mn89h/PiezoTestplatform/Presentation/Präsentation.pdf

Elektro- und Informationstechnik | Integrierte Elektronische Systeme | Malte Nilges

# DESIGN AND DEVELOPMENT OF A CUSTOM ASIC TEST PCB FOR ULTRASONIC COMMUNICATION

# Project seminar by

# Malte Nilges

12.08.2023 | 1

# OVERVIEW

# - Piezoelectric transducers for sensor communication and energy harvesting

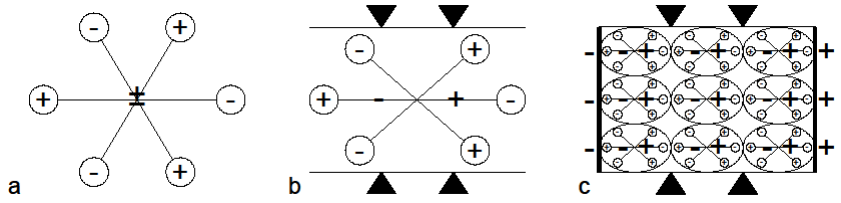
[picture p25: figure]

# - Aim of this work:

# - Piezo driver platform for data transmission and reception → hardware platform (PCB) → software platform (FPGA logic)

12.08.2023

C U S T O M A S I C T E S T P C B F O R U L T R A S O N I C C O M M U N I C A T I O N / M A L T E N I L G E S

# PCB DESIGN

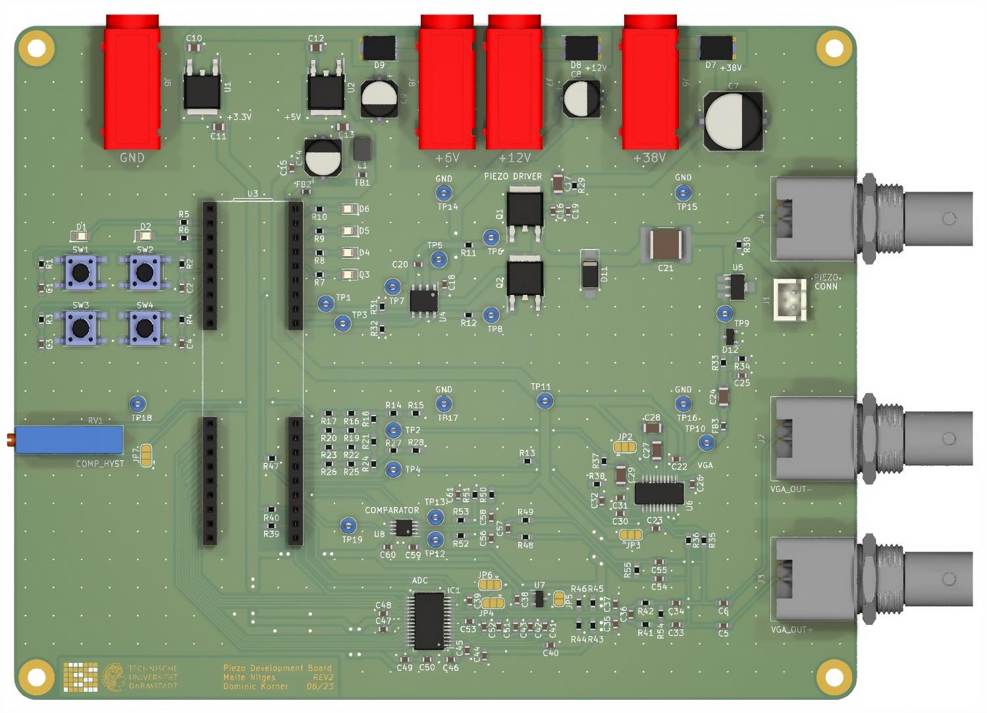
[picture p26: figure]

# PCB DESIGN

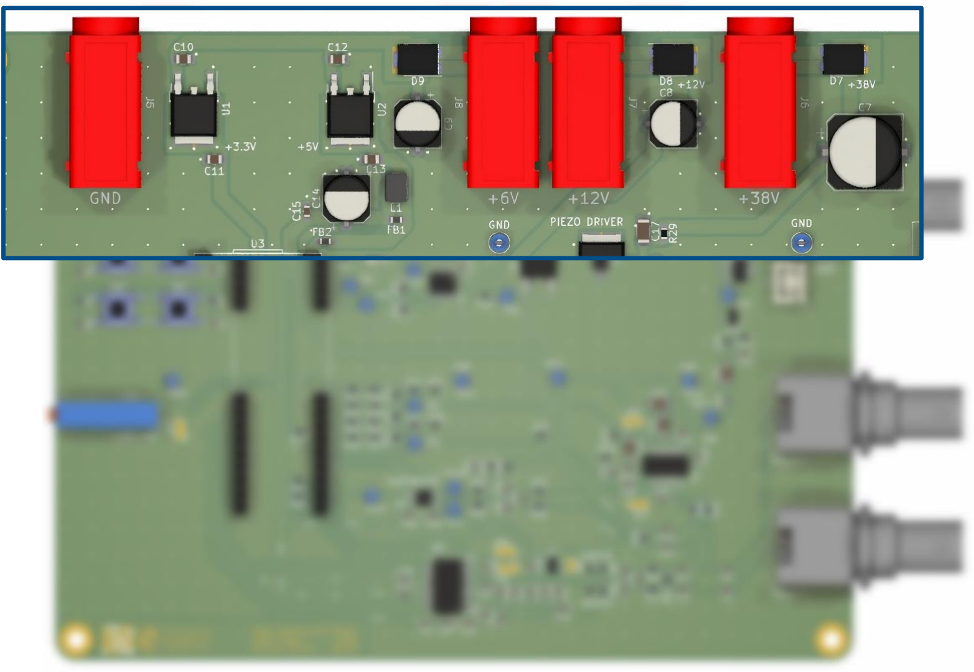
[picture p27: figure]

# Power stage:

# - Rails: 3.3V, 5VA, 5VD, 12V, 38V

# - NCP1117 3.3V & 5V LDO

# - 3 connectors

# - Reverse polarity protection diodes

# PCB DESIGN

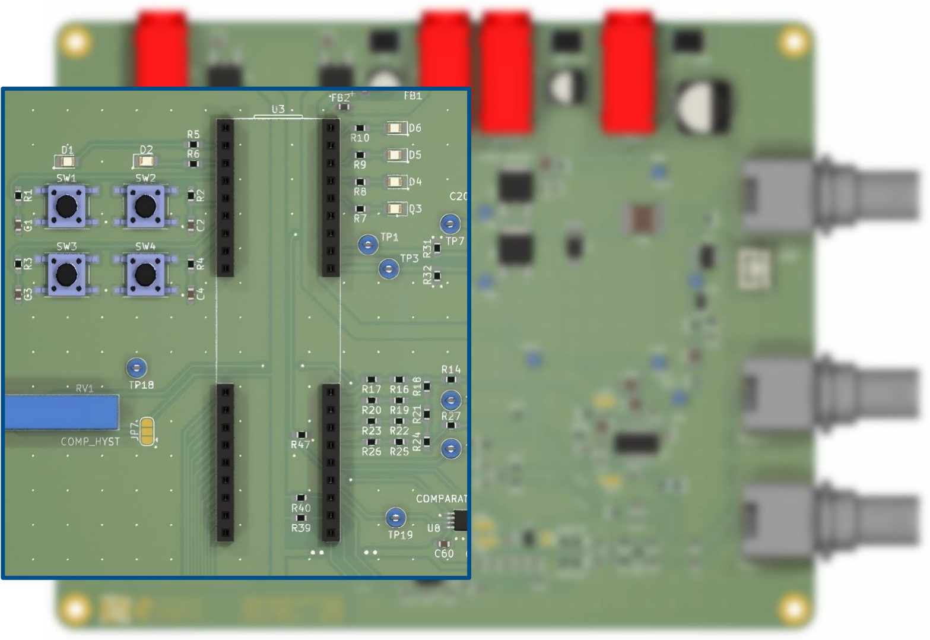
[picture p28: figure]

# FPGA & I/O:

# - CMOD S7 (Spartan XC7S25)

# - Push Buttons

# - LEDs

# - DAC

# PCB DESIGN

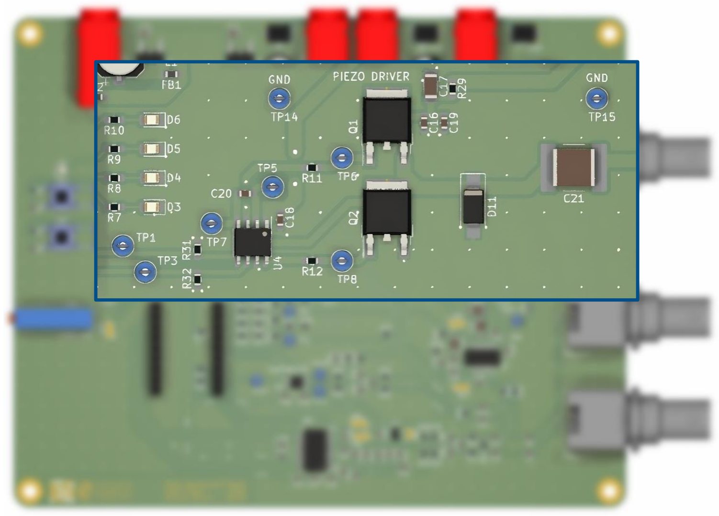
[picture p29: figure]

# Piezo driver stage:

# - MIC4604 half-bridge gate driver

# - 2x FDD1600N10ALZ NMOS

# - TVS diode

# - AC-coupled output

# PCB DESIGN

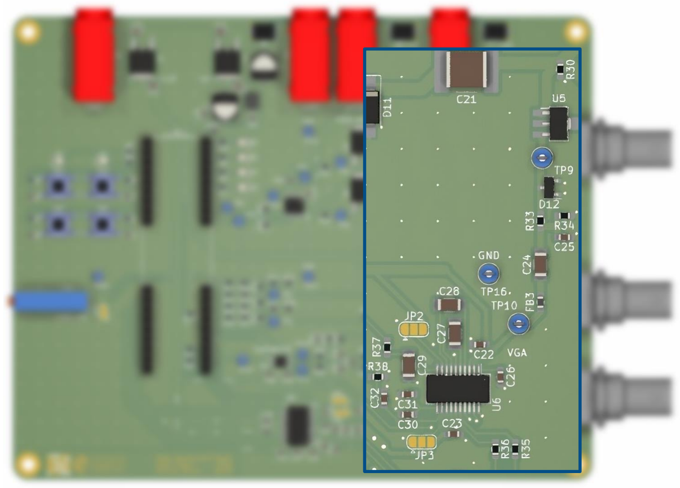
[picture p30: figure]

# Piezo input & amplifier stage:

# - MD0100 T/R switch

# - BAV99 protection diodes

# - Filtering network

# - AD8331 Low-Noise Amplifier with Variable Gain Amplifier

# PCB DESIGN

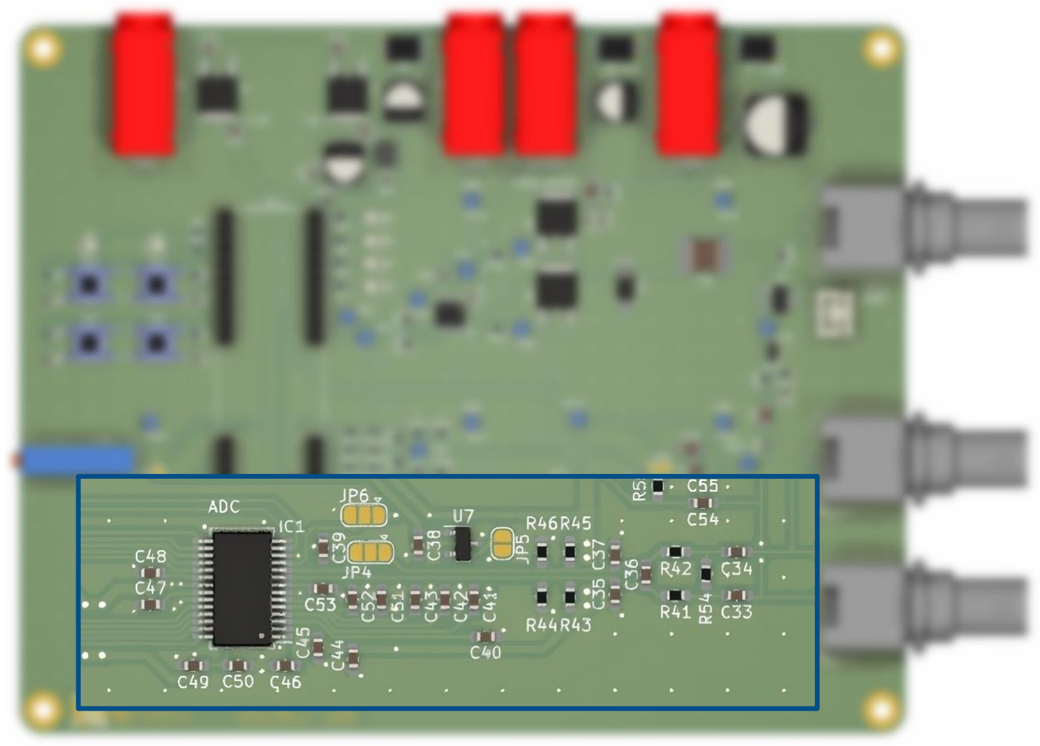
[picture p31: figure]

# ADC stage:

# - AC-coupled

# - Low-pass filter network

# - MAX1426 10bit 10MHz ADC

# - Internal biasing; Vpp,diff = 4V

# PCB DESIGN

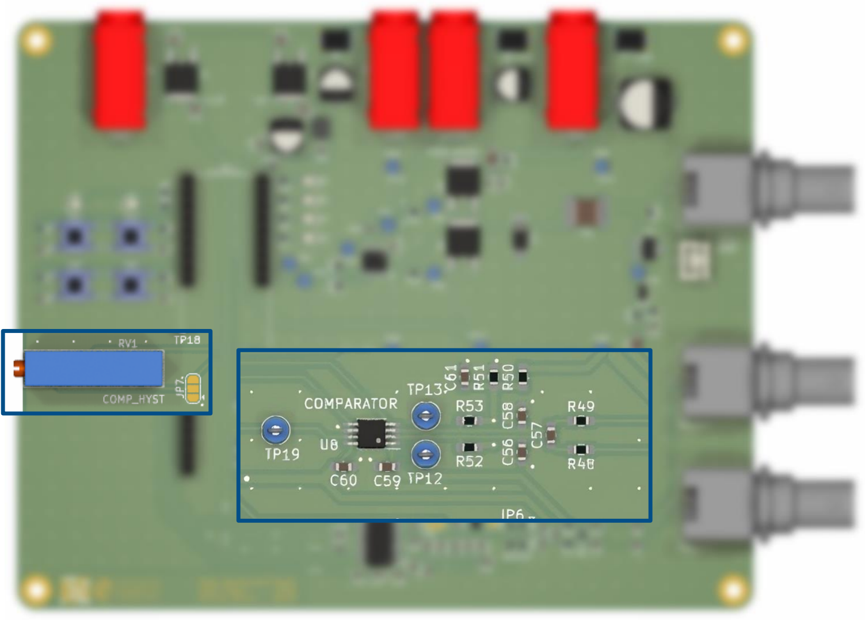
[picture p32: figure]

# Comparator stage:

# - AC-coupled

# - Band-pass filter network

# - LTC6752 280MHz comparator

# - External biasing

# - Adjustable hysteresis

# FPGA MODULES

# Main modules:

# - comm_protocol

# - vga_driver

# - comp_driver

# - adc_driver

Helper modules: | Imported modules:

# FPGA MODULES

# Helper modules:

# - piezo_driver

# - delay

# - fifo_aggregate

# - fifo_x2byte

# - pulse_stretcher

# - serial_tx_handler

# - serial_rx_handler

# - buttons_handler

# Main modules:

# - comm_protocol

# - vga_driver

# - comp_driver

# - adc_driver

# Imported modules:

# FPGA MODULES

# Helper modules:

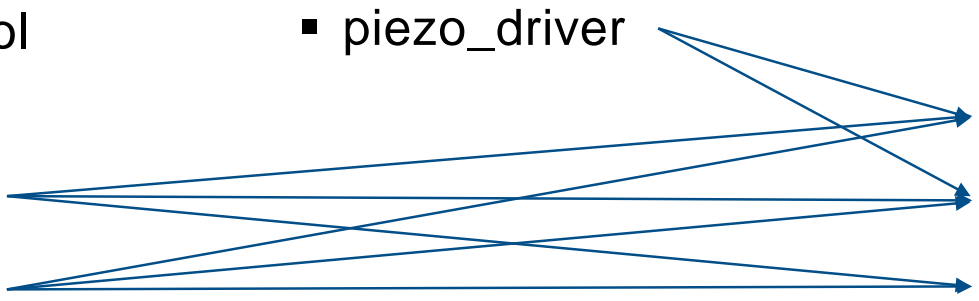
[picture p33: figure]
▪ piezo_driver

# - serial_tx_handler

# - serial_rx_handler

# Main modules:

# - comm_protocol

# - vga_driver

# - comp_driver

# - adc_driver

# Imported modules:

# - mmcme2_*

# - xpm_cdc_*

# - xpm_fifo_async

# - uart_tx

# - uart_rx

# RESULTS – TRANSMISSION

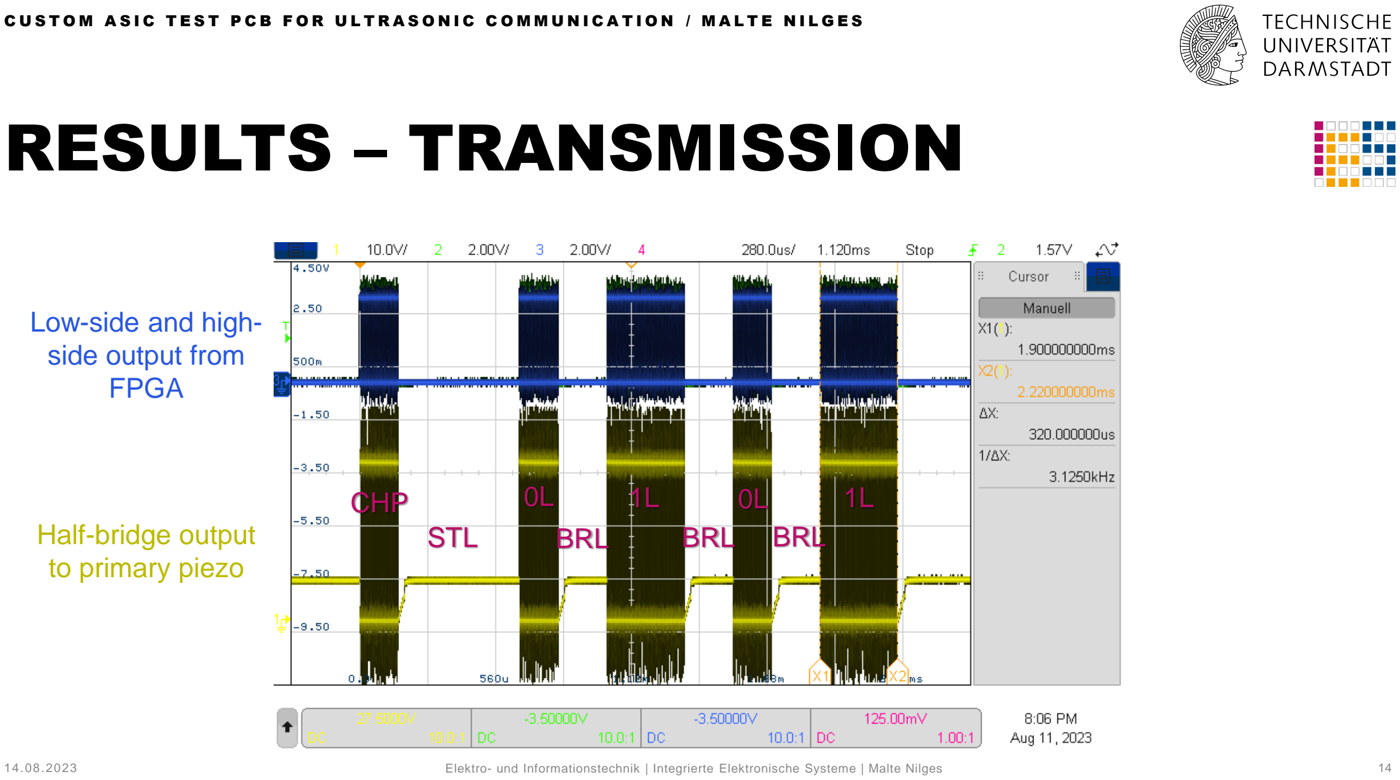
[picture p34: page 13]

# CHP STL

0L | 0L
BRL | BRL
1L | 1L
Half-bridge output | BRL

# to primary piezo

# Low-side and high-side output from FPGA

# RESULTS – TRANSMISSION

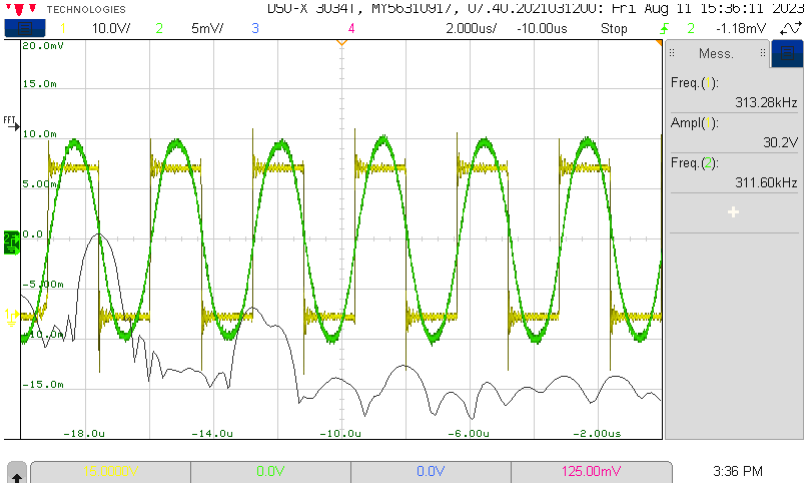
[picture p35: figure]

# Half-bridge output to primary piezo

# Secondary piezo output

# RESULTS – VGA

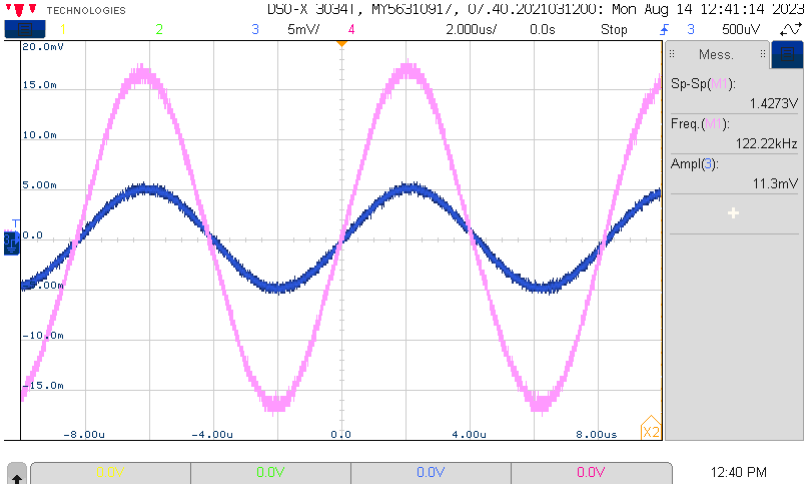
[picture p36: figure]

# Amplified differential output signal

10 mV

# input signal

# RESULTS – ADC

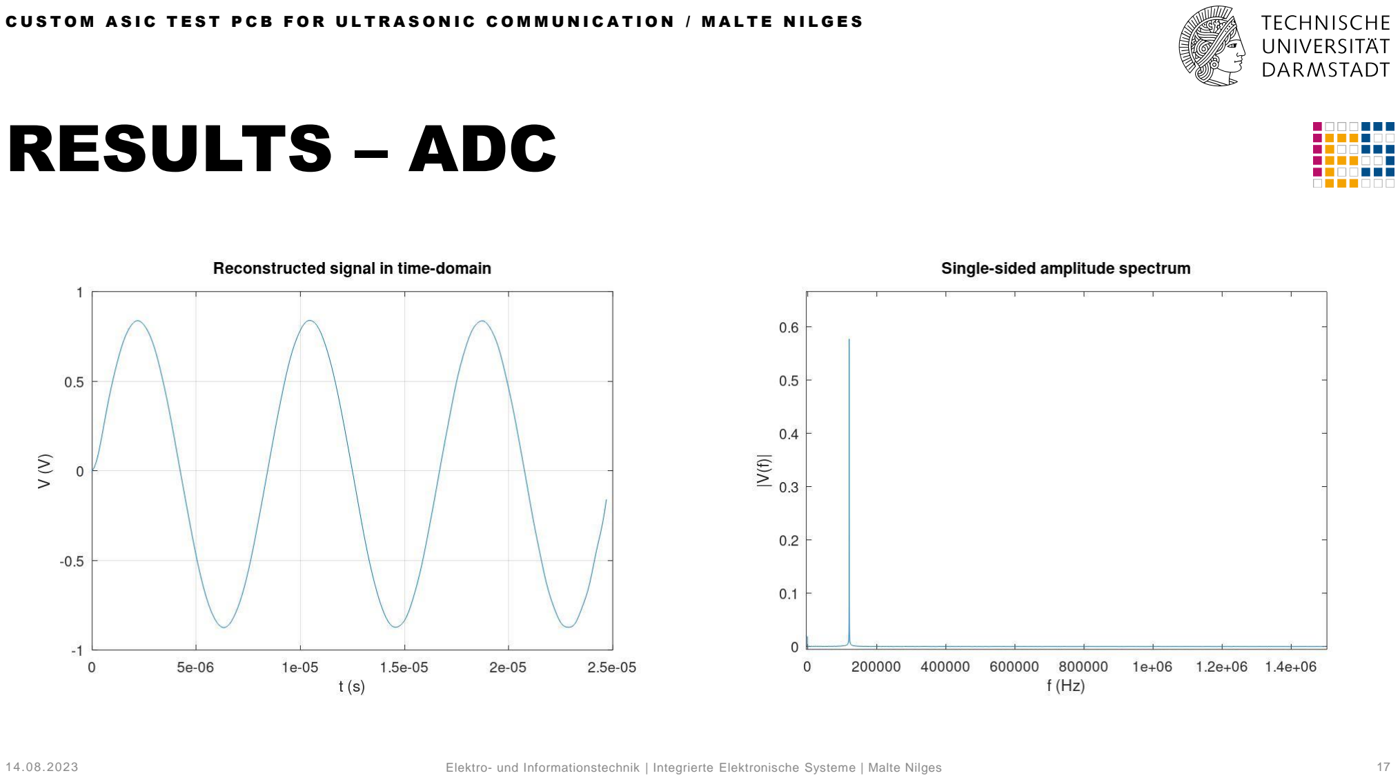
[picture p37: page 16]

# CONCLUSION

# - Hardware platform:

# - Drives piezo at specified loads (38 V, 100 Ω load, 2 MHz switching frequency) - Sampling of up to 5 MHz signals (ADC) or up to 25 MHz (comparator)

# - Software platform:

# - OOK transmission scheme - Variable sampling frequency and bit width

# - Possible improvements:

# - Increased host communication speed - Other transmission schemes
