mn89h/PiezoTestplatform/Report/samples/sig_time_long.pdf

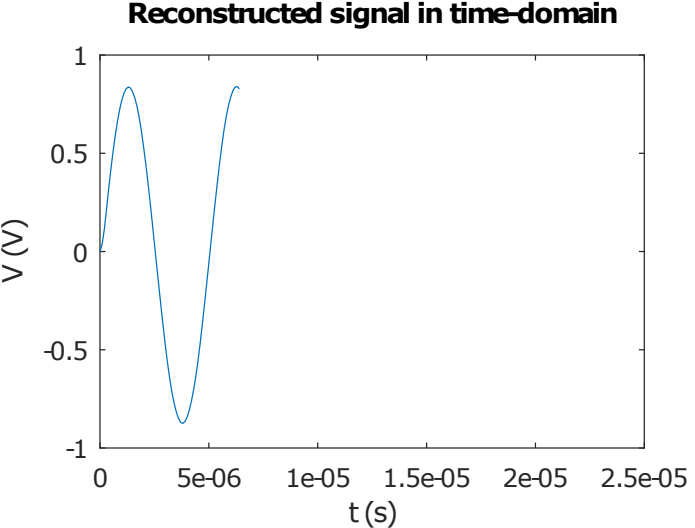
[picture p38: figure]
Reconstructed signal in time-domain
