mn89h/PiezoTestplatform/Piezo_TestPlatform/misc/adc_force_test.png

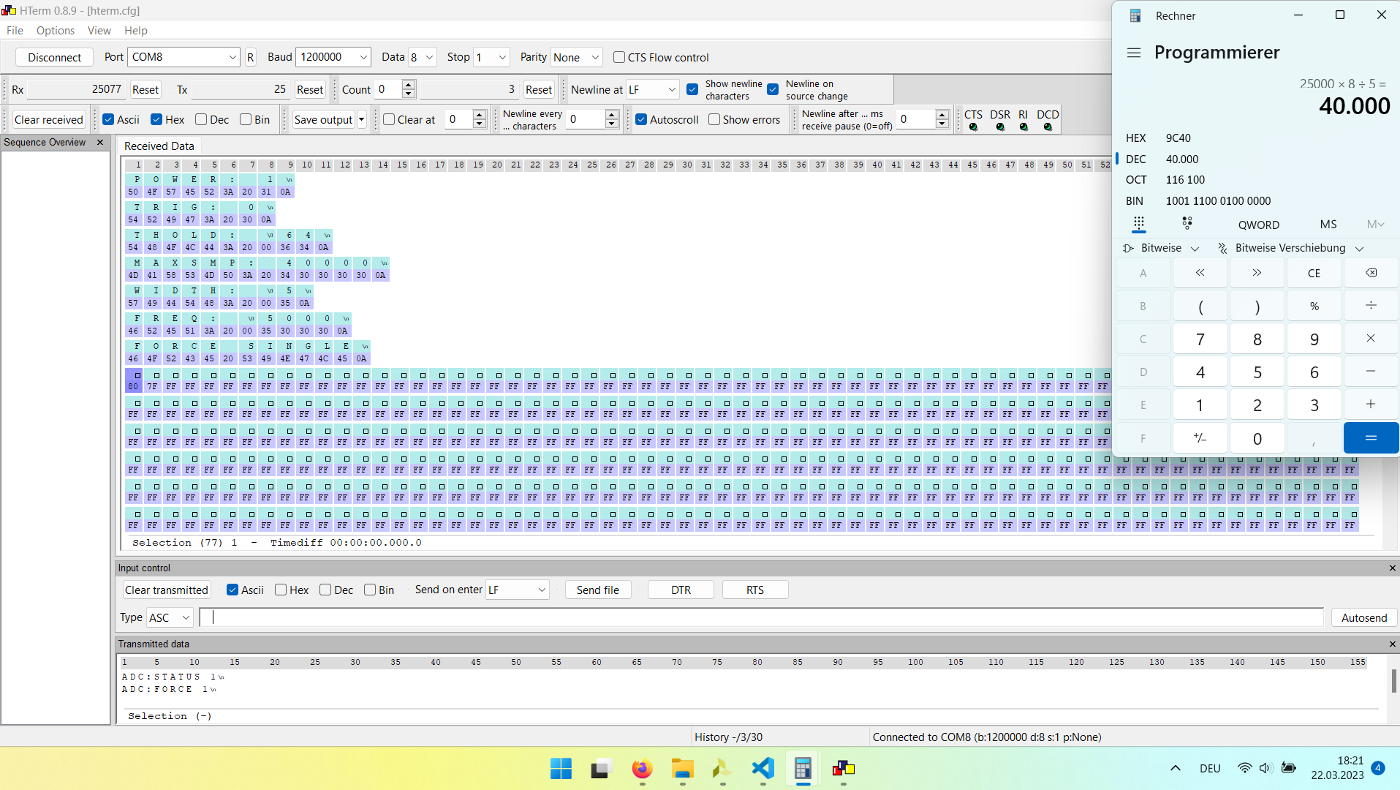
Piezo_TestPlatform/misc/adc_force_test.png
