mn89h/PiezoTestplatform/Report/samples/plot15_7-inc.pdf

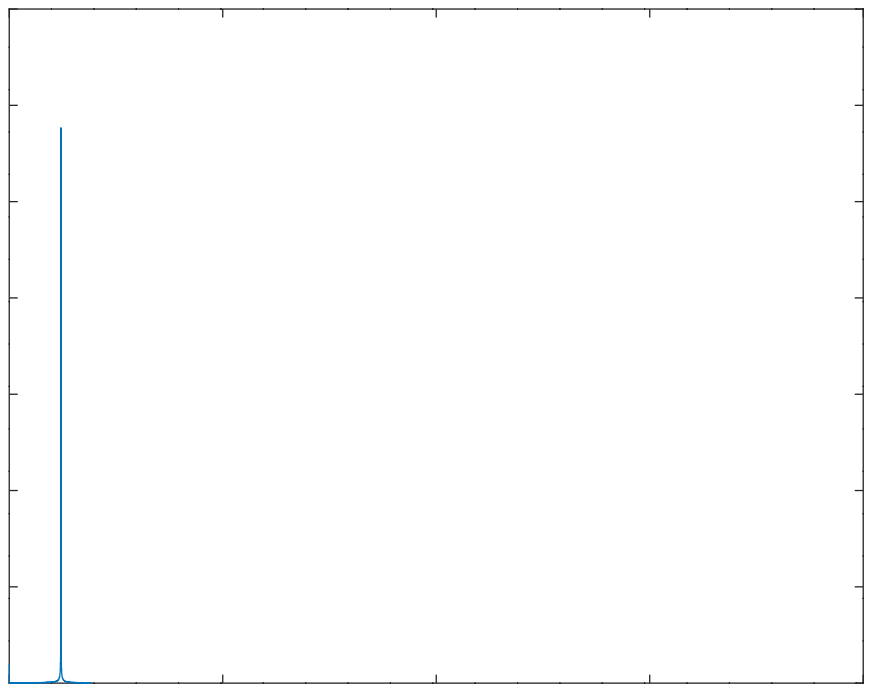
[picture p48: page 1]
