mn89h/PiezoTestplatform/Report/samples/sig_freq_long.pdf

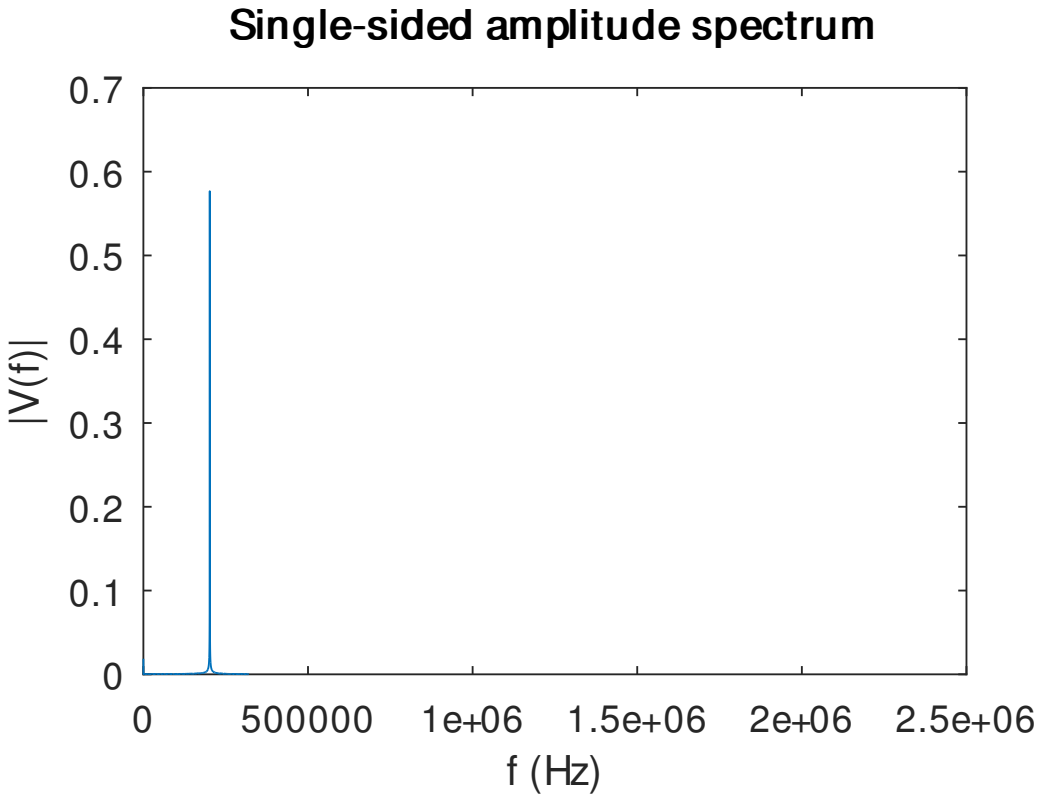
[picture p49: page 1]

Sin g le-sided am plit u de spect ru m
