mn89h/PiezoTestplatform/Report/sims/piezo_inout.asc

C1: cap; 1µ; V=200 Irms=0 Rser=0 Lser=0
C2: cap; 13p
C3: cap; 10n
D1: diode
D2: diode
D3: diode
D4: diode
M1: nmos; IRF2805S
R1: res; 100
R2: res; 100K
R3: res; 1Meg
R4: res; 1
R5: res; 100Meg
V1: signal; SINE(0 10 4.3Meg); AC 100
V2: voltage; 0
V3: voltage; SINE(0 1.5 4.2Meg)
X1: PiezoElement; L=0.5m S=1e-4
X2: SubstInf; d=7.9K V=5.17K
X3: SubstFin
X4: SubstInf; d=7.9K V=5.17K
X5: PiezoElement; L=0.5m S=1e-4
Named nets: 0, Tx, TxRx, Rx
Iron
Water
;tran 0 50u 0 0.5n
PZT-5
Iron
.tran 1u
