mn89h/PiezoTestplatform/Report/sims/piezodriver1.asc

C1: cap; 1n
C2: cap; 1n
C3: cap; 100n
C4: cap; 2f
C5: cap; 80f
D1: diode
L1: ind; 0.1
M1: nmos; IRF2805S
M2: nmos; IRF2805S
R1: res; 50
R2: res; 100m
R3: res; 1k
R4: res; 1k
R5: res; 1k
R6: res; 1k
S1: sw; MYSWITCH
U1: UniversalOpAmp2; Avol=1Meg GBW=100Meg Slew=100Meg
U3: UniversalOpAmp2; Avol=1Meg GBW=100Meg Slew=1000Meg; Ilimit=100m Rail=0 Vos=0
V1: voltage; 5
V2: voltage; PWL(0 0 100n 0 110n 30); Rser=3
V3: voltage; 2
V4: voltage; PULSE(0 4 5n 5n 5n 80n 200n)
V5: voltage; PULSE(3.2 0 0 5n 5n 90n 200n)
V7: voltage; PULSE(0 4 5n 5n 5n 80n 200n)
V8: voltage; 5
Named nets: 0
.model MYSWITCH SW (Ron=1n Roff=1MEG Vt=10n Vh=0.5)
.tran 1u
