mn89h/PiezoTestplatform/Report/sims/symbols/PiezoElement.asc

C0: cap; {C0}
C1: cap; 1
E1: e; 1
F1: f; V1 {h1}
F2: f; V2 {h2}
O1: ltline; Tpzt
R1: res; 1K
V1: voltage; 0
V2: voltage; 0
Named nets: B, F, E+, E-, i_deform, 0
.model Tpzt LTRA(len={L} R={Rt} L={Lt} C={Ct})
* PZT-5A
.param d=7750; (Kg/m3)
.param Q=75
.param V=4350; (m/s)
.param eS=7.35e-9; (C2/Nm2)
.param e33=15.8; (C/m2)
Ultrasonic Transducer by J.Deventer. 
LTspice adaptation by Kubov V.I.
* Model
.param C0=eS*S/L; (F)
.param Lt=d*S; (H) 
.param Ct=1/(V**2*Lt); (F)
.param f0=V/(2*L); (Hz)
.param Rt=2*Pi*f0*Lt/Q; (Ohm)
.param h1=e33/eS 
.param h2=h1*C0
.params L=435u S=1.267e-4
