mn89h/PiezoTestplatform/Report/sims/symbols/SubstFin.asc

Load: ltline; Tload
Named nets: B, F, 0
.model Tload LTRA(len={L} R={Rt} L={Lt} C={Ct})
* Water
.param d=1000; (Kg/m3)
.param V=1500; (m/s)
.param Nv=1e-3; Viscosity(Pas)
* Model
.param Lt=d*S; (H) 
.param Ct=1/(V**2*Lt); (F)
.param Af2=8*Pi**2*Nv/(3*d*V**3); (Neper/m/Hz2)
.param At=Af2*F**2; (Neper/m)
.param Rt=2*V*d*S*At; (Ohm)
.params L=10m S=1e-4 
.param F=1Meg
