mn89h/PiezoTestplatform/Report/sims/symbols/SubstInf.asc

R1: res; {Z}
Named nets: B, 0
* Water
.param d=1000; (Kg/m3)
.param V=1500; (m/s)
* Model
.param Z=V*d*S; (Ohm)
.param S=1e-4; (m2)
