mn89h/PiezoTestplatform/Report/sims/symbols/TestEcho.asc

D1: diode
D2: diode
D3: diode
D4: diode
R1: res; 100
R2: res; 100K
V1: signal; PULSE(0 100 1u 1n 1n 1u)
X1: PiezoElement; L=0.5m S=1e-4
X2: SubstInf; d=7.9K V=5.17K
X3: SubstFin
X4: SubstInf; d=7.9K V=5.17K
Named nets: 0, Tx, TxRx, Rx
Iron
Water
.tran 0 50u 0 0.5n
PZT-5
Iron
