mn89h/PiezoTestplatform/Report/sims/symbols/TestRezonatorAir.asc

R1: res; 100
V1: signal; SINE(0 1 4.34Meg); AC 1
X1: PiezoElement; L=0.5m S=1e-4
X2: SubstInf; d=1.3 V=300
X3: SubstInf; d=1.3 V=300
Named nets: 0, Tx, TxRx
Air
.ac dec 10000 1Meg 50Meg
PZT-5
Air
