mn89h/PiezoTestplatform/Piezo_TestPlatform/Piezo_TestPlatform.srcs/sim_1/uart_ascii_helper.v

task send_ascii_A;
    begin
        #(10*PERIOD); uart_rx = 0;
        #(10*PERIOD); uart_rx = 1;
        #(10*PERIOD); uart_rx = 0;
        #(10*PERIOD); uart_rx = 0;
        #(10*PERIOD); uart_rx = 0;
        
        #(10*PERIOD); uart_rx = 0;
        #(10*PERIOD); uart_rx = 0;
        #(10*PERIOD); uart_rx = 1;
        #(10*PERIOD); uart_rx = 0;
        #(10*PERIOD); uart_rx = 1;
    end
endtask

task send_ascii_B;
    begin
        #(10*PERIOD); uart_rx = 0;
        #(10*PERIOD); uart_rx = 0;
        #(10*PERIOD); uart_rx = 1;
        #(10*PERIOD); uart_rx = 0;
        #(10*PERIOD); uart_rx = 0;
        
        #(10*PERIOD); uart_rx = 0;
        #(10*PERIOD); uart_rx = 0;
        #(10*PERIOD); uart_rx = 1;
        #(10*PERIOD); uart_rx = 0;
        #(10*PERIOD); uart_rx = 1;
    end
endtask

task send_ascii_C;
    begin
        #(10*PERIOD); uart_rx = 0;
        #(10*PERIOD); uart_rx = 1;
        #(10*PERIOD); uart_rx = 1;
        #(10*PERIOD); uart_rx = 0;
        #(10*PERIOD); uart_rx = 0;
        
        #(10*PERIOD); uart_rx = 0;
        #(10*PERIOD); uart_rx = 0;
        #(10*PERIOD); uart_rx = 1;
        #(10*PERIOD); uart_rx = 0;
        #(10*PERIOD); uart_rx = 1;
    end
endtask

task send_ascii_D;
    begin
        #(10*PERIOD); uart_rx = 0;
        #(10*PERIOD); uart_rx = 0;
        #(10*PERIOD); uart_rx = 0;
        #(10*PERIOD); uart_rx = 1;
        #(10*PERIOD); uart_rx = 0;
        
        #(10*PERIOD); uart_rx = 0;
        #(10*PERIOD); uart_rx = 0;
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
        #(10*PERIOD); uart_rx = 0;
        #(10*PERIOD); uart_rx = 1;
        
        #(10*PERIOD); uart_rx = 1;
        #(10*PERIOD); uart_rx = 1;
        #(10*PERIOD); uart_rx = 0;
        #(10*PERIOD); uart_rx = 0;
        #(10*PERIOD); uart_rx = 1;
    end
endtask
